Juani005999/SQMLite/sources/ASCOM.SQMLite.ObservingConditions/Resources/SQMLite.jpg

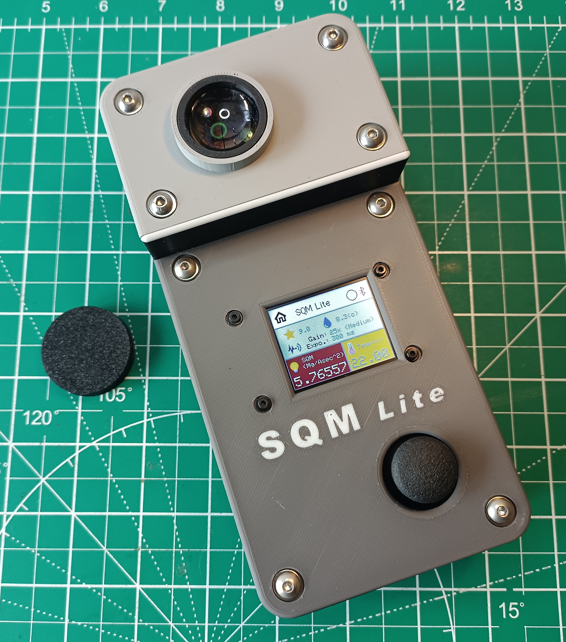
sources/ASCOM.SQMLite.ObservingConditions/Resources/SQMLite.jpg
