Juani005999/SQMLite/sources/SQMLite/Examples/SQMLite/SQMLite.ino

/// ---------------------------------------------------------------------
///
/// Projet                          : SQM Lite - Sky Quality Meter
/// Auteur                          : Juanito del Pepito
/// Version                         : 2.0.1.0
/// Date                            : 31/05/2026
/// 
/// Description                     : Sky Quality Meter (SQM)
/// Gitub                           : https://github.com/Juani005999/SQMLite
/// Licence							            : GPL-3.0 license
///
/// Configuration                   : Les paramètres de configuration de l'application se trouvent dans le fichier suivant
///                                   <Arduino librairies> -> SQMLite -> src -> SQMLITE_APP_CONFIG.h
///
/// Capteurs et périphériques       : Cette application utilise les capteurs et périphériques suivant
///										                - TSL2591
///										                - BME280
///										                - TFT ST7735
/// 
/// Prérequis                       : Cette application nécessite l'ajout des bibliothèques suivantes
///										                - Adafruit_TSL2591
///										                - Adafruit_BME280
///										                - TFT_eSPI
/// 
/// ---------------------------------------------------------------------
#include <SQMLITE_APP.h>

// Instanciation des objets internes
SQMLITE_APP app = SQMLITE_APP();

void setup()
{
  // Initialisation SerialPort
  Serial.begin(115200);
  while(!Serial);

  // Initialisation de l'application
  app.Init();
}

void loop()
{
  // Exécution du processus Loop de l'application
  app.Loop();
}
